sparkfun/SparkFun_Qwiic_WAV_Trigger_Pro/docs/assets/img/WAV_Trigger_Pro-Audio.jpg

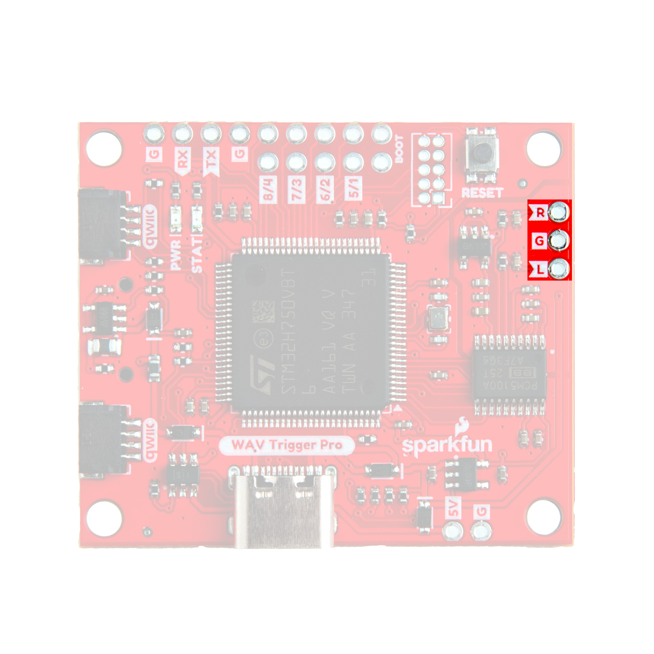
docs/assets/img/WAV_Trigger_Pro-Audio.jpg
