sparkfun/SparkFun_Qwiic_WAV_Trigger_Pro/docs/assets/img/WAV_Trigger_Pro-Triggers.jpg

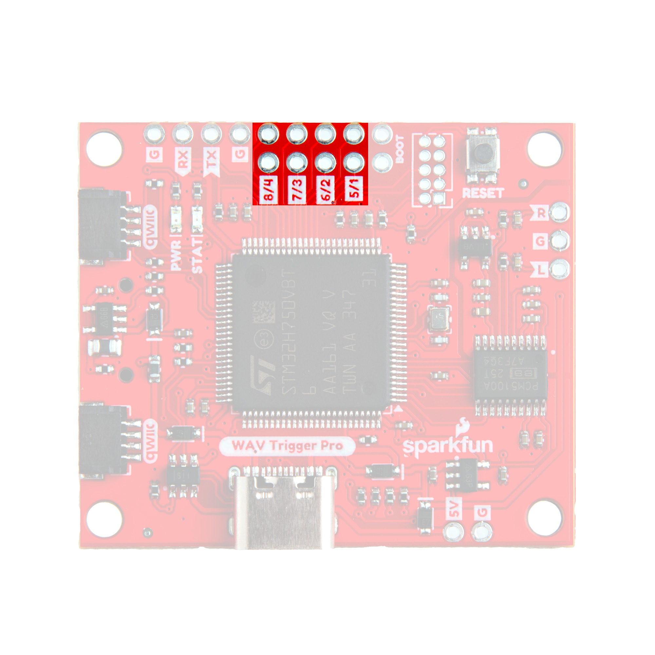
docs/assets/img/WAV_Trigger_Pro-Triggers.jpg
